warhog/fpvlaptracker/firmware/statemanager.h

#pragma once

#include <Arduino.h>

//#define DEBUG

namespace statemanagement {

    enum class state_enum {
        STARTUP,
        CALIBRATION,
        CALIBRATION_DONE,
        SCAN,
        DEEPSCAN,
        RACE,
        RESTORE_STATE,
        ERROR,
        VREF_OUTPUT,
        SWITCH_TO_BLUETOOTH
    };

    class StateManager {
    public:
        StateManager() : _state(state_enum::STARTUP), _storeState(state_enum::STARTUP) {
        }

        String toString(state_enum state) {
            if (state == state_enum::CALIBRATION || state == state_enum::CALIBRATION_DONE) {
                return "Calibration";
            } else if (state == state_enum::RACE) {
                return "Race";
            } else if (state == state_enum::ERROR) {
                return "Error";
            } else if (state == state_enum::SCAN) {
                return "Scan";
            } else if (state == state_enum::DEEPSCAN) {
                return "Deep scan";
            } else if (state == state_enum::STARTUP) {
                return "Startup";
            } else if (state == state_enum::VREF_OUTPUT) {
                return "VREF output";
            } else if (state == state_enum::SWITCH_TO_BLUETOOTH) {
                return "switch to bluetooth mode";
            } else {
#ifdef DEBUG
                Serial.printf("unknown state: %d\n", state);
#endif
                return "Unknown";
            }
        }

        boolean isStateStartup() {
            return this->_state == state_enum::STARTUP;
        }

        boolean isStateCalibration() {
            return this->_state == state_enum::CALIBRATION;
        }

        boolean isStateCalibrationDone() {
            return this->_state == state_enum::CALIBRATION_DONE;
        }

        boolean isStateScan() {
            return this->_state == state_enum::SCAN;
        }

        boolean isStateDeepscan() {
            return this->_state == state_enum::DEEPSCAN;
        }

        boolean isStateError() {
            return this->_state == state_enum::ERROR;
        }

        boolean isStateRace() {
            return this->_state == state_enum::RACE;
        }

        state_enum getState() {
            return this->_state;
        }

        void setState(state_enum state) {
            if (state != this->_state) {
#ifdef DEBUG
                Serial.print(F("change state to "));
                Serial.println(this->toString(state));
#endif
                this->storeState();
                this->_state = state;
            }
        }

        void storeState() {
            this->_storeState = this->_state;
#ifdef DEBUG
            Serial.print(F("stored state "));
            Serial.println(this->toString(this->_storeState));
#endif
        }
        
        void restoreState() {
            this->_state = this->_storeState;
        }

        void update(state_enum state){
            if (state == state_enum::RESTORE_STATE) {
#ifdef DEBUG
                Serial.print(F("restore state request to "));
                Serial.println(this->toString(this->_storeState));
#endif
                this->setState(this->_storeState);
                return;
            }
#ifdef DEBUG
            Serial.print(F("state change request to "));
            Serial.println(this->toString(state));
#endif
            this->setState(state);
        }
        
    private:
        state_enum _state;
        state_enum _storeState;

    };

}
